MelyGalvez/MAPA/Gestion de projet/Fonctionnal_Diagram/Fonctionnal_Diagram.png

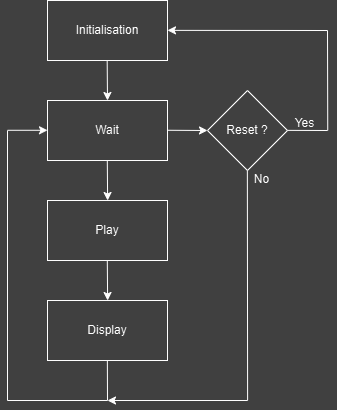
Gestion de projet/Fonctionnal_Diagram/Fonctionnal_Diagram.png
