MelyGalvez/MAPA/Gestion de projet/Fonctionnal_Diagram/Modeling.png

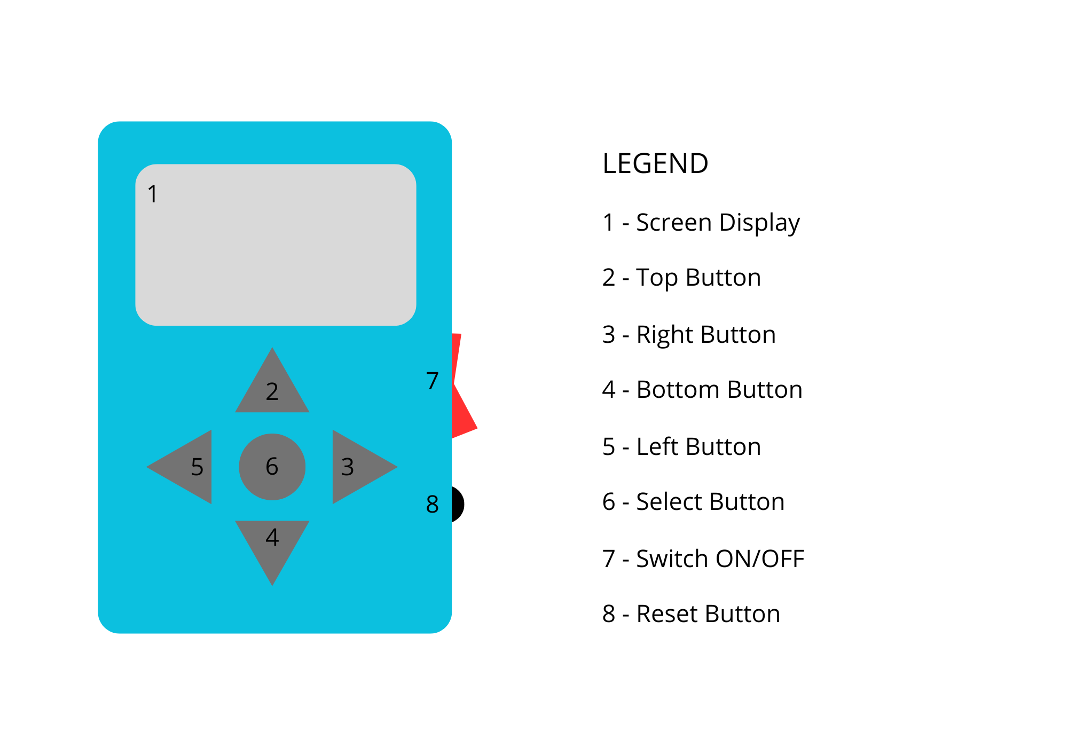
Gestion de projet/Fonctionnal_Diagram/Modeling.png
