MelyGalvez/MAPA/Gestion de projet/Initialisation/Initialisation des rubans led MAPA.png

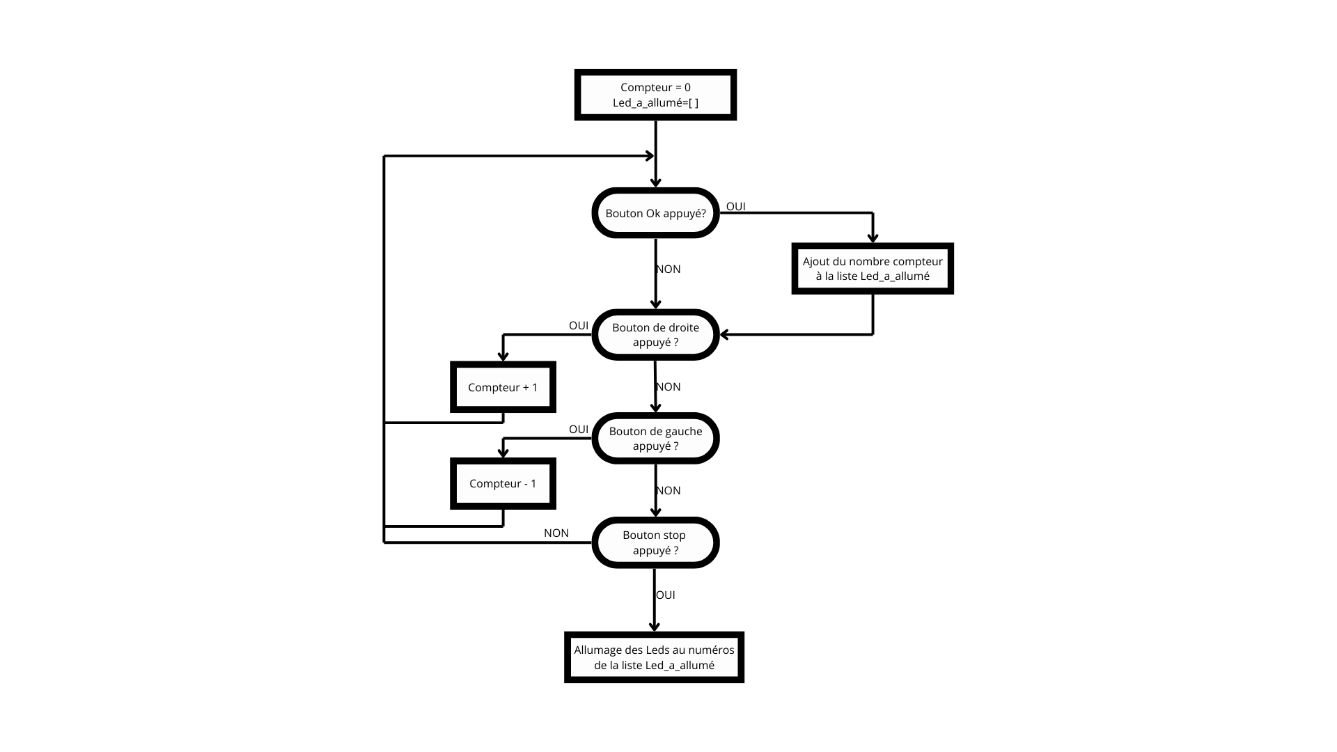
Gestion de projet/Initialisation/Initialisation des rubans led MAPA.png
