MelyGalvez/MAPA/Gestion de projet/Traitement du signal audio/Fonctionnal_Diagram_DSP/Fonctionnal_Diagram_DSP.png

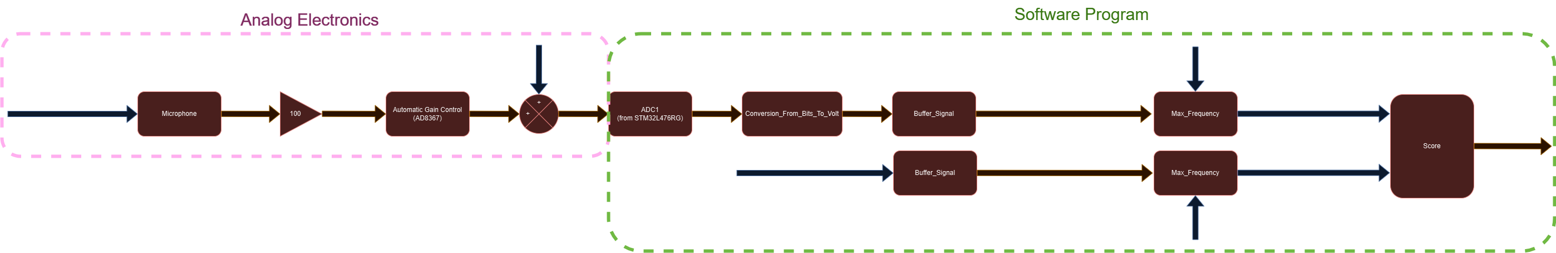
Gestion de projet/Traitement du signal audio/Fonctionnal_Diagram_DSP/Fonctionnal_Diagram_DSP.png
