MelyGalvez/MAPA/Gestion de projet/Traitement fichier MIDI/Fonctionnal_Diagram/Functionnal_Diagram.png

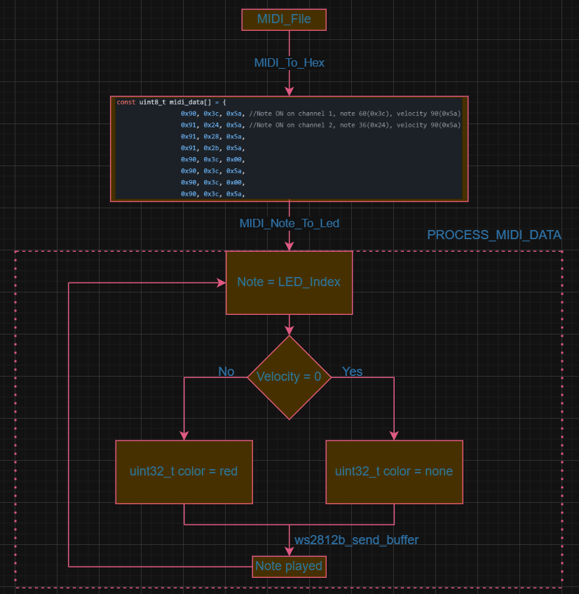
Gestion de projet/Traitement fichier MIDI/Fonctionnal_Diagram/Functionnal_Diagram.png
