MelyGalvez/MAPA/Traitement numérique du signal du micro/Etude des complexités spatiales et temporelles/Résultats/Complexite_Spatiale_Fin.png

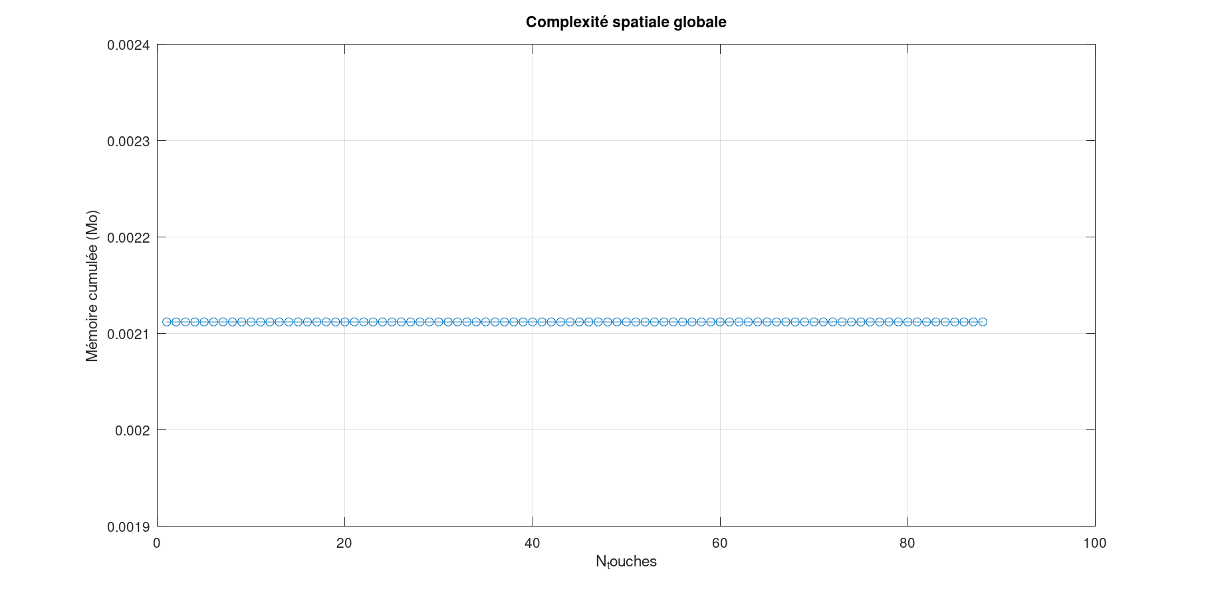
Traitement numérique du signal du micro/Etude des complexités spatiales et temporelles/Résultats/Complexite_Spatiale_Fin.png
