MelyGalvez/MAPA/Traitement numérique du signal du micro/Etude des sons du piano/Résultats/DSP_pour_un_La4.png

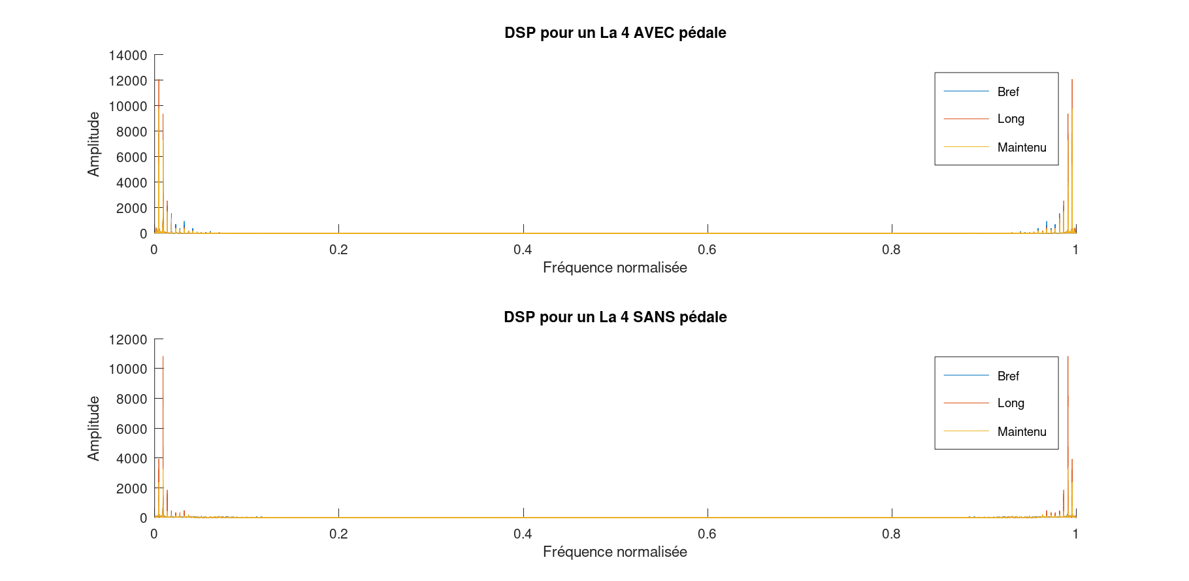
Traitement numérique du signal du micro/Etude des sons du piano/Résultats/DSP_pour_un_La4.png
