MelyGalvez/MAPA/Traitement numérique du signal du micro/Etude des sons du piano/Résultats/Signaux_temporels_pour_un_accord.png

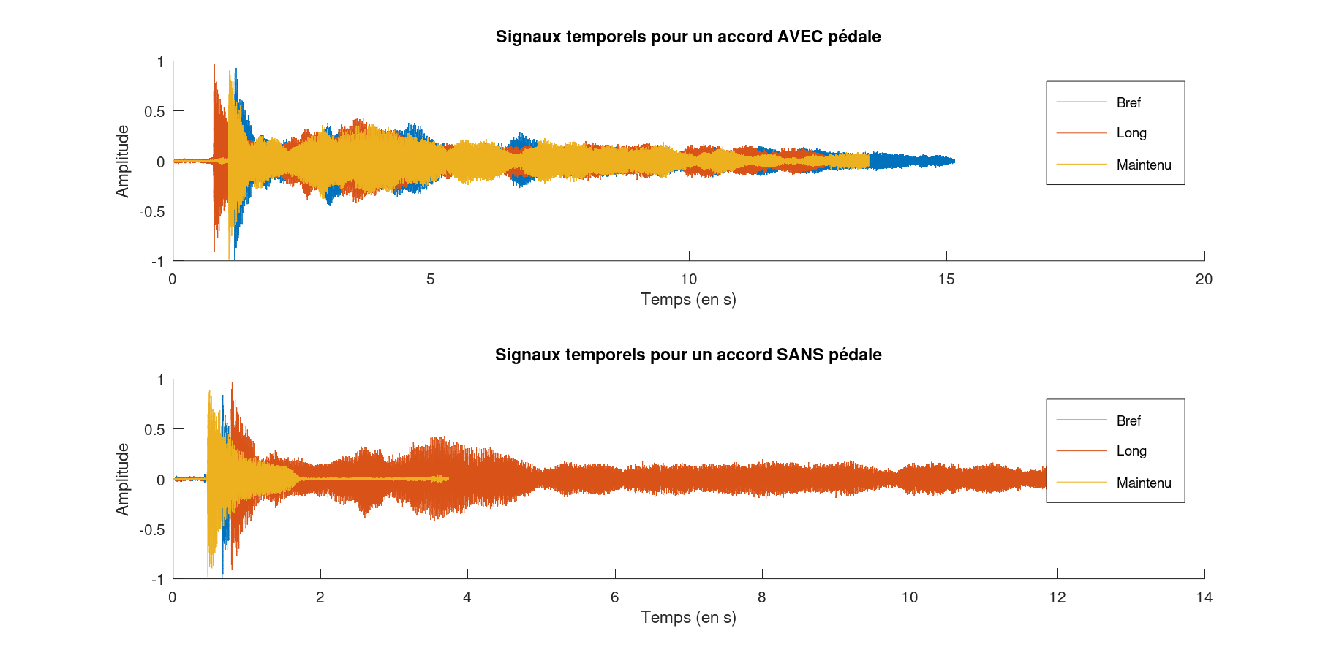
Traitement numérique du signal du micro/Etude des sons du piano/Résultats/Signaux_temporels_pour_un_accord.png
