MelyGalvez/MAPA/Gestion de projet/Fonctionnal_Diagram/Components Diagram.png

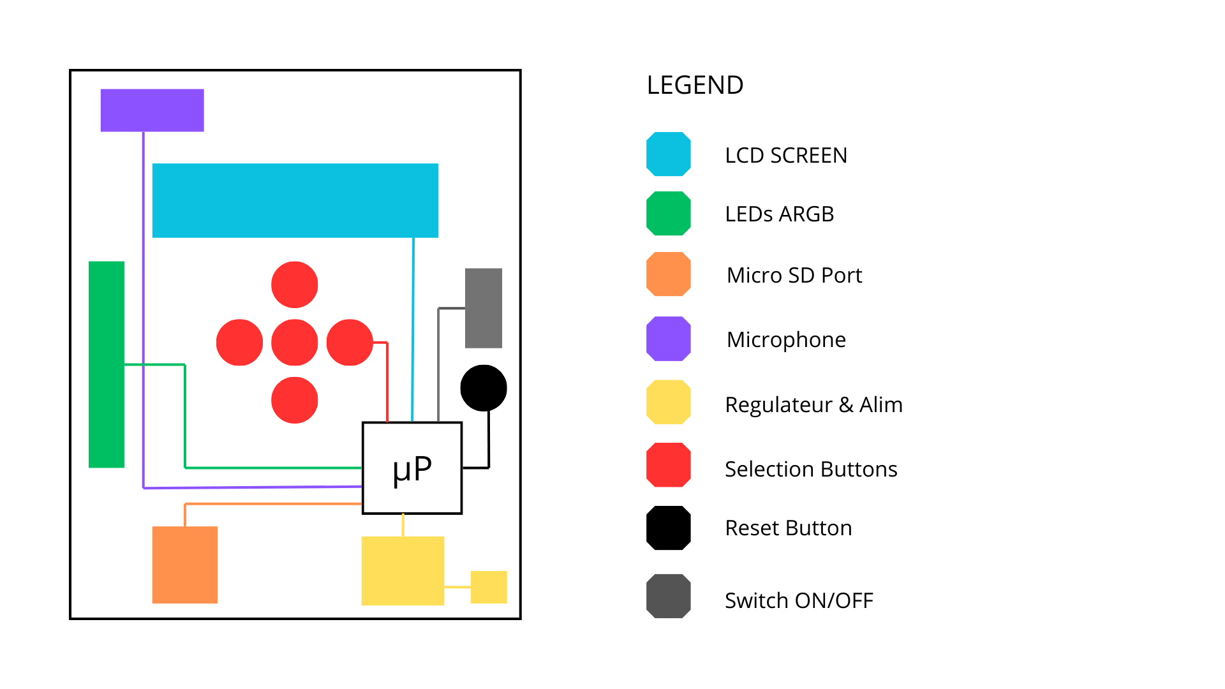
Gestion de projet/Fonctionnal_Diagram/Components Diagram.png
