MelyGalvez/MAPA/Initialisation + Midi/Inc/menu.h

/*
 * menu.h
 *
 *  Created on: Mar 11, 2025
 *      Author: lijia
 */

#ifndef INC_MENU_H_
#define INC_MENU_H_

extern const char *menu_principal[];

void Navigation();
void LCD_DisplayMenu();
void LCD_DisplaySousMenu();
#endif /* INC_MENU_H_ */
